riedoninc/smart_shunt_meter/Images/IMG_7711.JPG

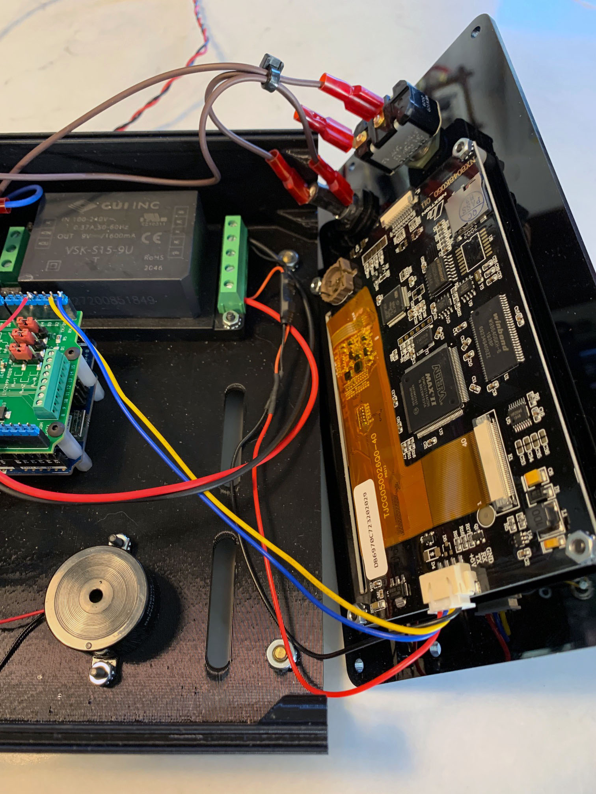
Images/IMG_7711.JPG
