riedoninc/smart_shunt_meter/Images/IMG_7712.JPG

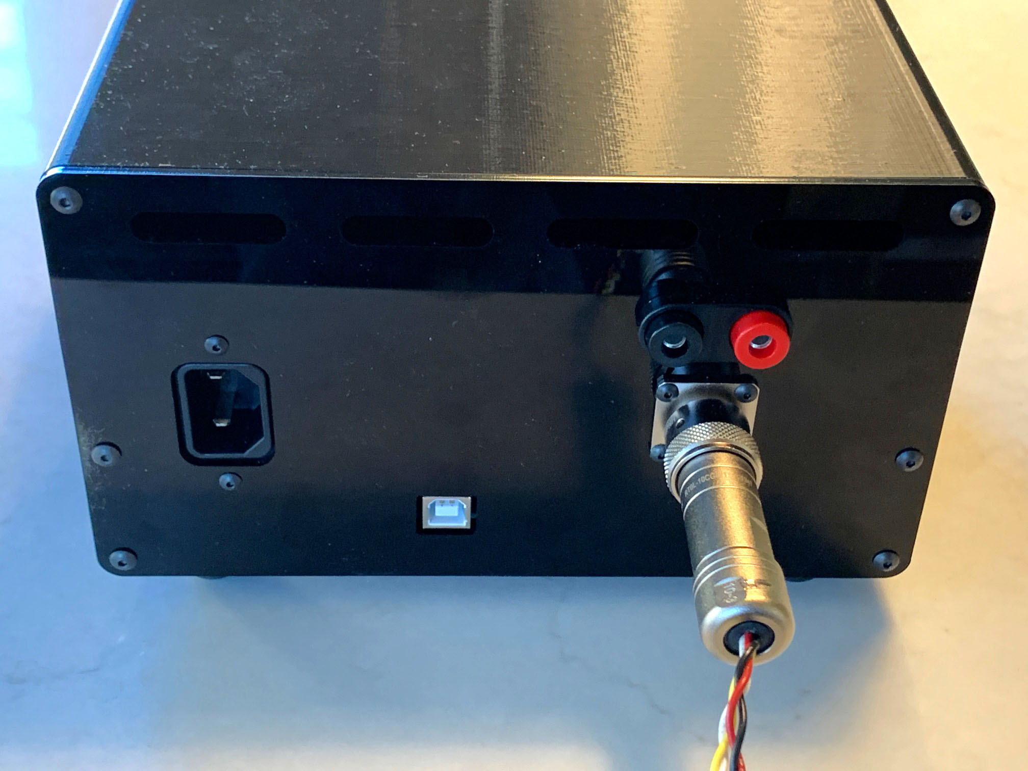
Images/IMG_7712.JPG
