riedoninc/smart_shunt_meter/Images/IMG_7713.JPG

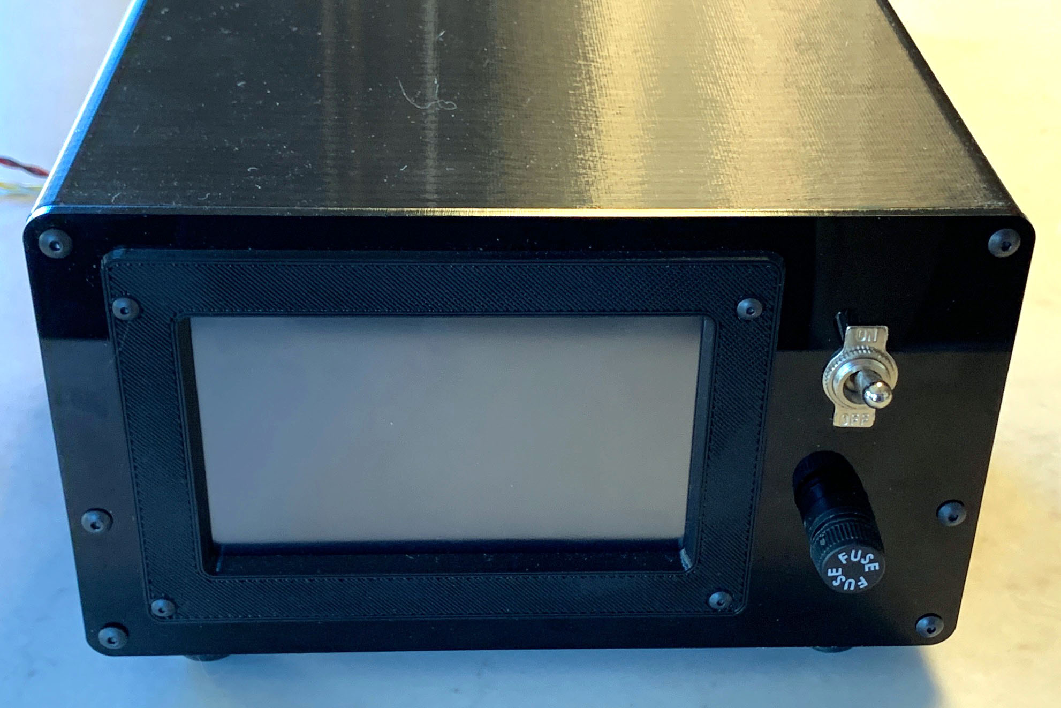
Images/IMG_7713.JPG
