riedoninc/smart_shunt_meter/Images/IMG_7714.JPG

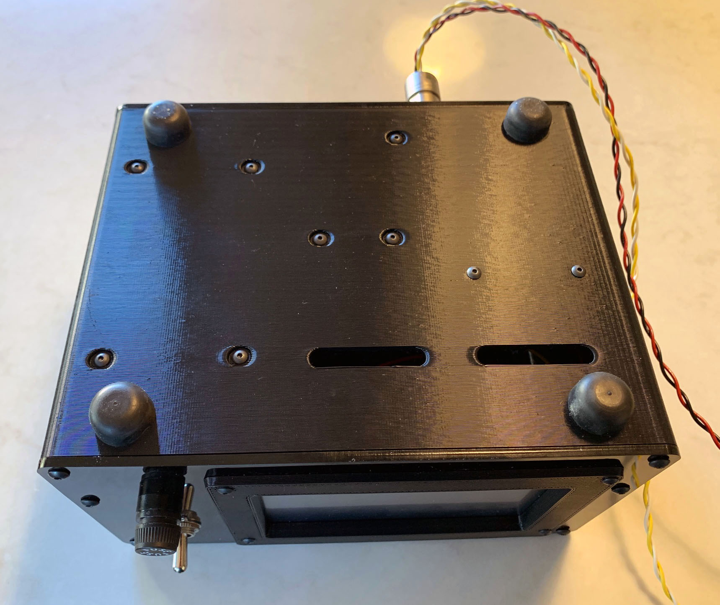
Images/IMG_7714.JPG
