riedoninc/smart_shunt_meter/Nextion Display/Home Pressed.png

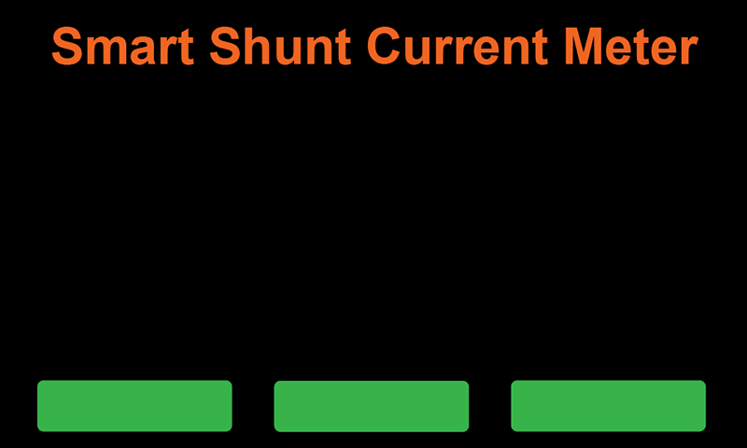
Nextion Display/Home Pressed.png
