riedoninc/smart_shunt_meter/Nextion Display/Lowercase Data Entry.png

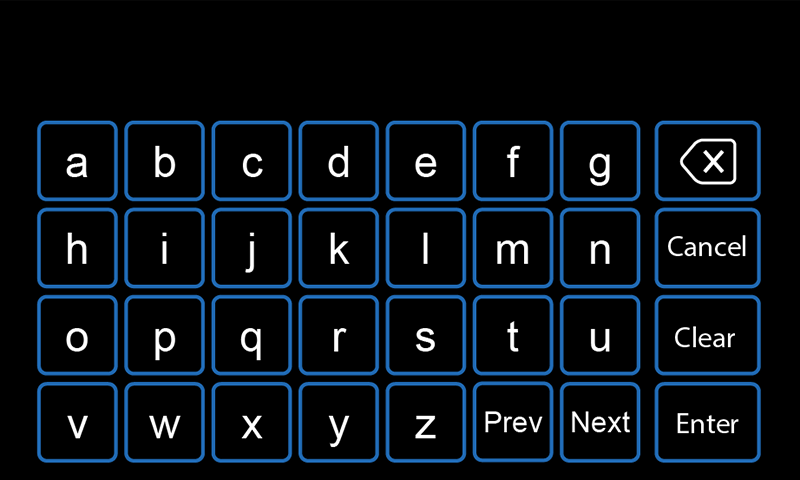
Nextion Display/Lowercase Data Entry.png
