riedoninc/smart_shunt_meter/Nextion Display/Uppercase Data Entry.png

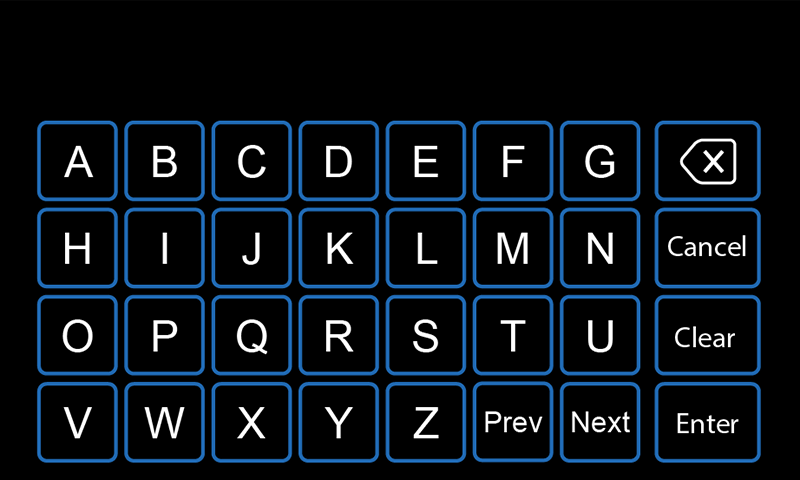
Nextion Display/Uppercase Data Entry.png
