riedoninc/smart_shunt_meter/CAD/STEP/CUI_vsk-t cover.step

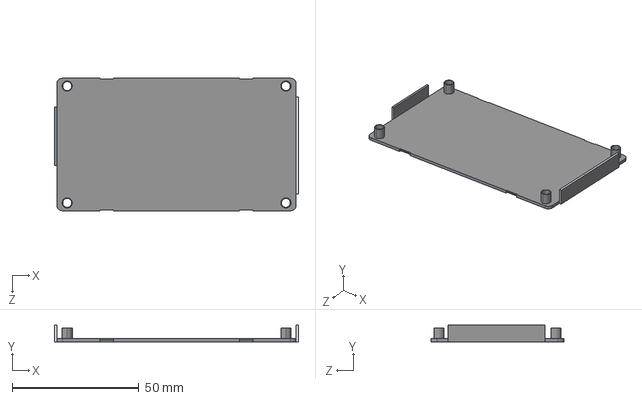
[picture p29: CAD file, 2021-02-21]
CAD/STEP/CUI_vsk-t cover.step
96.1 x 6.50 x 52.2 mm
