riedoninc/smart_shunt_meter/CAD/STEP/CUI_vsk-s15 series.step

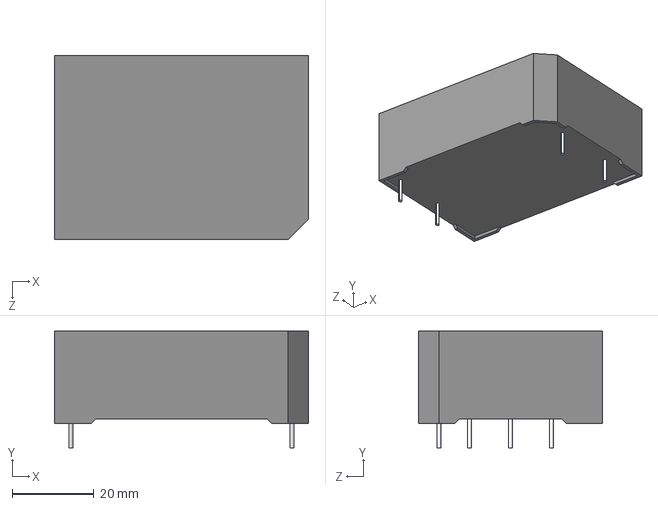
[picture p30: CAD file, 2021-02-21]
CAD/STEP/CUI_vsk-s15 series.step
62.0 x 28.5 x 45.0 mm
