riedoninc/smart_shunt_meter/CAD/STEP/NEXTION NX8048T050 Bezel.step

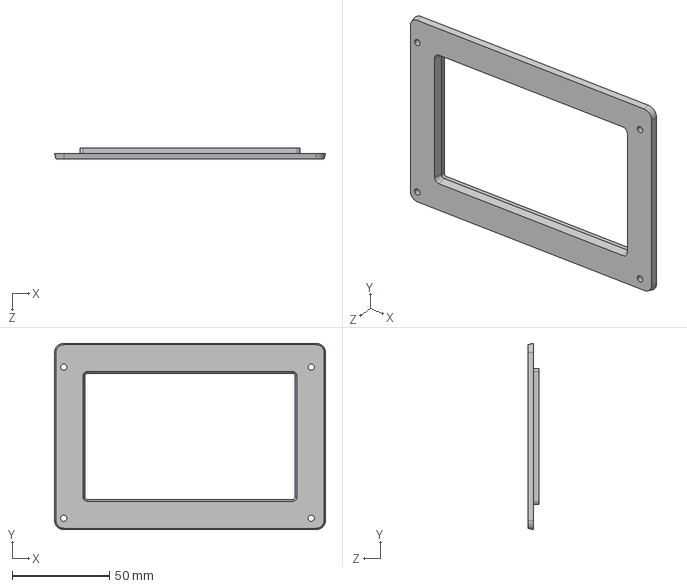
[picture p31: CAD file, 2021-02-21]
CAD/STEP/NEXTION NX8048T050 Bezel.step
139.2 x 95.7 x 5.84 mm
