riedoninc/smart_shunt_meter/CAD/STEP/ARD-LTC2499.step

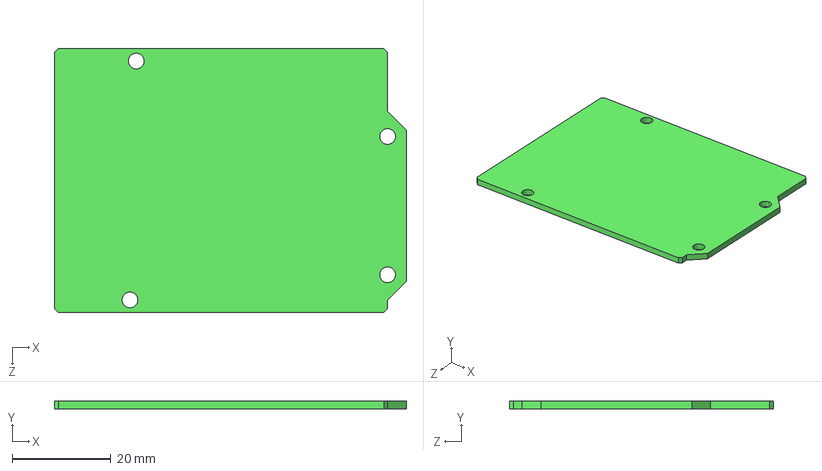
[picture p32: CAD file, 2021-02-21]
CAD/STEP/ARD-LTC2499.step
71.1 x 1.60 x 53.3 mm
