riedoninc/smart_shunt_meter/CAD/STEP/9541K2_THREADED-STUD BUMPER.step

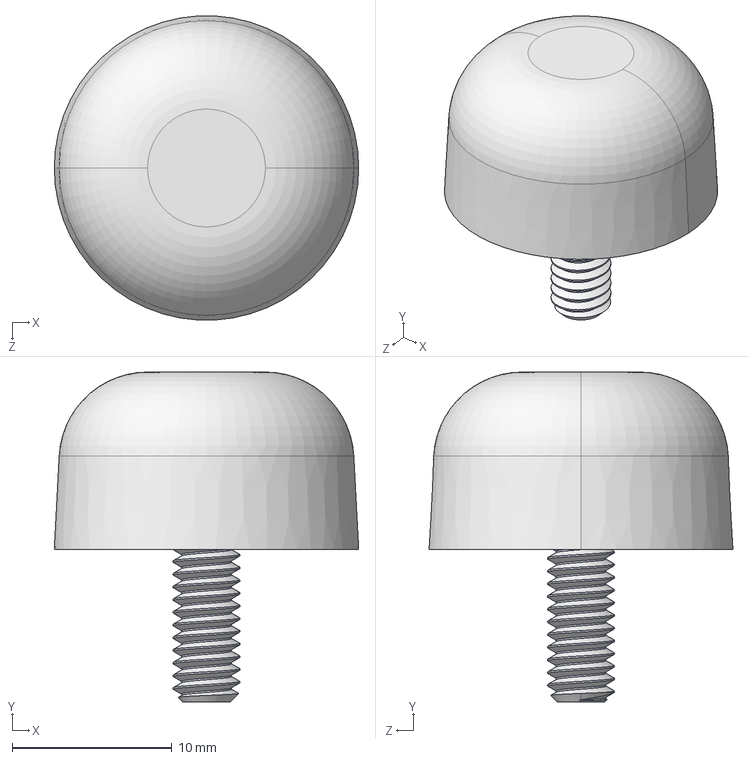
[picture p33: CAD file, 2021-02-21]
CAD/STEP/9541K2_THREADED-STUD BUMPER.step
19.1 x 20.6 x 19.0 mm
